89Mods/LVDC/Programs/System/interrupt.asm

	SECTION interrupt
	PUBLIC interrupt_handler_loop
	PUBLIC clear_trupt
	PUBLIC clear_keyrupt
	PUBLIC clear_rrupt
	PUBLIC interrupt_handler_loop_hopc
	PUBLIC temp_tripped
curr_mod equ 2
curr_sec equ 0
	org (curr_sec<<8)|(curr_mod<<12)
interrupt:
	STO +hop_save
	
	cdscurr
	PIO status_read
	AND temp_bit
	XOR temp_bit
	TNZ irupt_no_temp
	CLA temp_bit
	STO temp_tripped
irupt_no_temp:
	
	; Lets see - why are we here?
	; Loop until there are no more interrupts left to handle
interrupt_handler_loop:
	cdscurr
	PIO status_read
	AND clear_trupt
	TNZ enter_trupt_handler
	PIO status_read
	AND clear_keyrupt
	TNZ enter_keyrupt_handler
	PIO status_read
	AND clear_rrupt
	TNZ enter_rrupt_handler
	CLA temp_tripped
	TNZ enter_temp_handler
	TRA iret
enter_trupt_handler:
	HOP* trupt_handler
enter_keyrupt_handler:
	HOP* keyrupt_handler
enter_rrupt_handler:
	HOP* rrupt_handler
enter_temp_handler:
	HOP* temp_handler

iret:
	CLA bugfix
	CDSS 0,1
	ADD +hop_save
	STO +0
	PIO intclr
	PIO intclr
	HOP +0
bugfix:
	dd 1<<7
temp_tripped:
	dd 0
clear_trupt:
	dd (1 << 1)
clear_keyrupt:
	dd (1 << 0)
clear_rrupt:
	dd (1 << 2)
temp_bit:
	dd (1 << 3)
interrupt_handler_loop_hopc:
	HOPC interrupt_handler_loop, curr_mod, curr_sec

	ENDSECTION

	SECTION trupt_handler
	PUBLIC trupt_handler
curr_mod equ 2
curr_sec equ 1
	org (curr_sec<<8)|(curr_mod<<12)
	dd 0 ; Spacer for interrupt vector
trupt_handler:
	CLA one
	cdsspare
	ADD @system_timer
	STO @system_timer
	cdscurr

	; UPDATE DISPLAY
	; Toggle blink_state every few interrupts
	CLA blink_counter
	ADD one
	STO blink_counter
	XOR blink_counter_targ
	TNZ no_blink
	CL
	STO blink_counter
	CLA blink_state
	XOR one
	STO blink_state
no_blink:
	; Determine what should be displayed
	cdsspare
	CLA @entry_mode
	TNZ mod1
	TRA not_entry_mode
mod1:
	cdscurr
	CLA offset_entry
	TRA regs_selected
not_entry_mode:
	CLA @cmd_act
	TNZ mod2
	TRA not_cmd_act
mod2:
	cdscurr
	CL
	TRA regs_selected
not_cmd_act:
	; from major mode
	cdscurr
	CLA offset_mm
regs_selected:
	; Weird self-modifying code to do indexed addressing
	; using the offset in the accumulator
	ADD indexed_base
	STO selfmod_0
	ADD offset_one
	STO selfmod_1
	ADD offset_one
	STO selfmod_2
	cdsspare
selfmod_0:
	CLA @0
	cdscurr
	STO r1_temp
	cdsspare
selfmod_1:
	CLA @0
	cdscurr
	STO r2_temp
	cdsspare
selfmod_2:
	CLA @0
	cdscurr
	STO r_s_temp

	cdsspare
	CLA @gpio_mirror
	cdscurr
	AND gpio_clr_signs
	STO temp
	
	CLA r_s_temp
	AND one
	TNZ r1_is_signed
	TRA r1_is_not_signed
r1_is_signed:
	CLA r1_temp
	AND msb
	XOR msb
	TNZ r1_is_not_signed
	CLA temp
	ADD gpio_sign_r1
	STO temp
	CL
	SUB one
	XOR r1_temp
	ADD one
	STO r1_temp
r1_is_not_signed:
	CLA one
	SHL 1
	AND r_s_temp
	TNZ r2_is_signed
	TRA r2_is_not_signed
r2_is_signed:
	CLA r2_temp
	AND msb
	XOR msb
	TNZ r2_is_not_signed
	CLA temp
	ADD gpio_sign_r2
	STO temp
	CL
	SUB one
	XOR r2_temp
	ADD one
	STO r2_temp
r2_is_not_signed:
	
	CLA r1_temp
	PIO r1_lo
	SHR 2
	SHR 2
	SHR 2
	SHR 2
	SHR 2
	SHR 2
	SHR 2
	SHR 2
	PIO r1_hi
	
	CLA r2_temp
	PIO r2_lo
	SHR 2
	SHR 2
	SHR 2
	SHR 2
	SHR 2
	SHR 2
	SHR 2
	SHR 2
	STO temp2
	CLA r_s_temp
	AND dp_bits_mask
	SHL 2
	SHL 2
	SHL 2
	SHL 2
	SHL 2
	ADD temp2
	PIO r2_hi

	CLA blink_state
	TNZ skip_blink
	CLA one
	SHL 2
	AND r_s_temp
	TNZ r1_blink
	TRA r1_no_blink
r1_blink:
	CL
	SUB one
	XOR gpio_sign_r1
	AND temp
	ADD gpio_sign_r1
	STO temp
r1_no_blink:
	CLA one
	SHL 1
	SHL 2
	AND r_s_temp
	TNZ r2_blink
	TRA skip_blink
r2_blink:
	CL
	SUB one
	XOR gpio_sign_r2
	AND temp
	ADD gpio_sign_r2
	STO temp
skip_blink:
	
	cdsspare
	CLA @curr_mm
	cdscurr
	SHL 2
	SHL 2
	SHL 2
	SHL 2
	ADD mm_change
	PIO settings_reg
	
	CLA temp
	cdsspare
	STO @gpio_mirror
	PIO gpio_out
	
	CDSS 2,0
	CLA @clear_trupt
	PIO settings_reg
	HOP @interrupt_handler_loop_hopc

blink_counter:
	dd 0
blink_counter_targ:
	dd 3
one:
	dd 1
mm_change:
	dd r_chg_mm
blink_state:
	dd 0
r1_temp:
	dd 0
r2_temp:
	dd 0
r_s_temp:
	dd 0
offset_mm:
	dd 3<<5
offset_entry:
	dd 6<<5
offset_one:
	dd 1<<5
indexed_base:
	CLA @0
gpio_clr_signs:
	dd ~(gr_sign_r2 | gr_sign_r1)
gpio_sign_r1:
	dd gr_sign_r1
gpio_sign_r2:
	dd gr_sign_r2
temp:
	dd 0
temp2:
	dd 0
dp_bits_mask:
	dd $3<<4
msb:
	dd 1<<25
temp_tripped:
	dd 0

	ENDSECTION

	SECTION keyrupt_temp_handlers
	PUBLIC keyrupt_handler
	PUBLIC temp_handler
curr_mod equ 2
curr_sec equ 2
	org (curr_sec<<8)|(curr_mod<<12)
keyrupt_handler:

	CDSS 2,0
	CLA @clear_keyrupt
	PIO settings_reg
	cdscurr

	HOP* cmd_entry_reset

temp_handler:
	STO +hop_save
	
	CLA last_time
	cdsspare
	RSU @system_timer
	cdscurr
	TNZ temp_update_lamps
	TRA temp_not_last_time
temp_update_lamps:
	CLA temp_lamp_bit
	cdsspare
	XOR @const_all_ones
	AND @gpio_mirror
	cdscurr
	ADD temp_lamp_bit
	cdsspare
	STO @gpio_mirror
	PIO gpio_out
	CLA @system_timer
	cdscurr
	STO last_time
temp_not_last_time:
	
	cdsspare
	CLA @system_timer
	SHR 2
	cdscurr
	AND and_vals
	STO sid_step
	
	CLA +hop_save
	ADD bugfix
	STO +0
	HOP +0
bugfix:
	dd 1<<7
sid_step:
	dd 0
last_time:
	dd 0
and_vals:
	dd $0F
temp_lamp_bit:
	dd gr_lamp_temp

	ENDSECTION

	SECTION rrupt_handler
	PUBLIC rrupt_handler
curr_mod equ 2
curr_sec equ 3
	org (curr_sec<<8)|(curr_mod<<12)
rrupt_handler:

	CDSS 2,0
	CLA @clear_rrupt
	PIO settings_reg
	HOP @interrupt_handler_loop_hopc

	ENDSECTION
